derekfountain/zx-spectrum-lower-ram/__ATTIC/IMG_20221003_200314.jpg

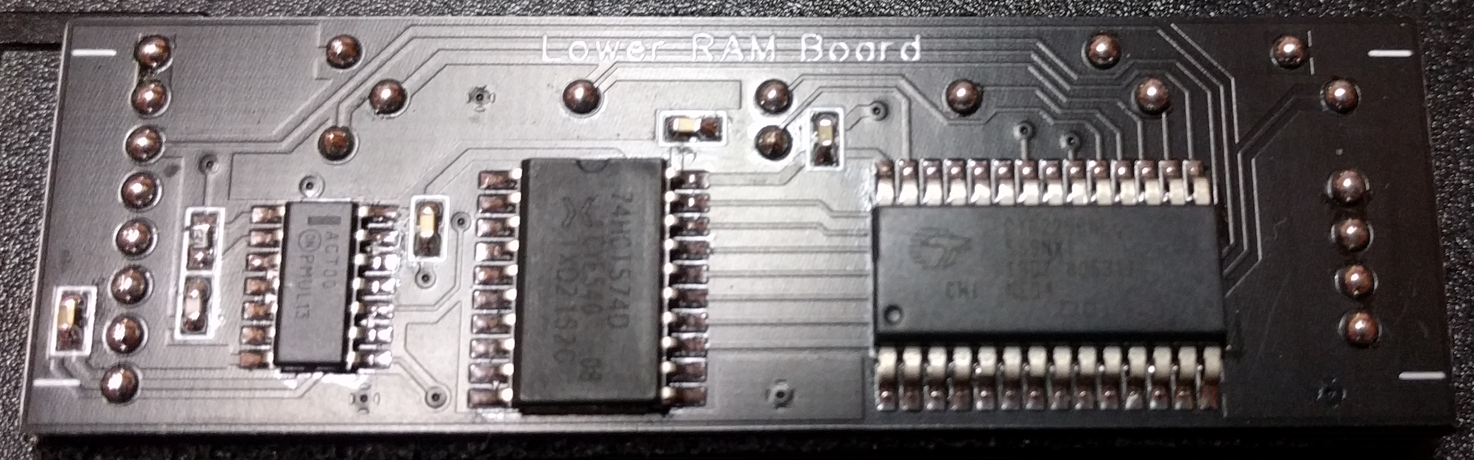
__ATTIC/IMG_20221003_200314.jpg
