derekfountain/zx-spectrum-lower-ram/__ATTIC/IMG_20221003_200335.jpg

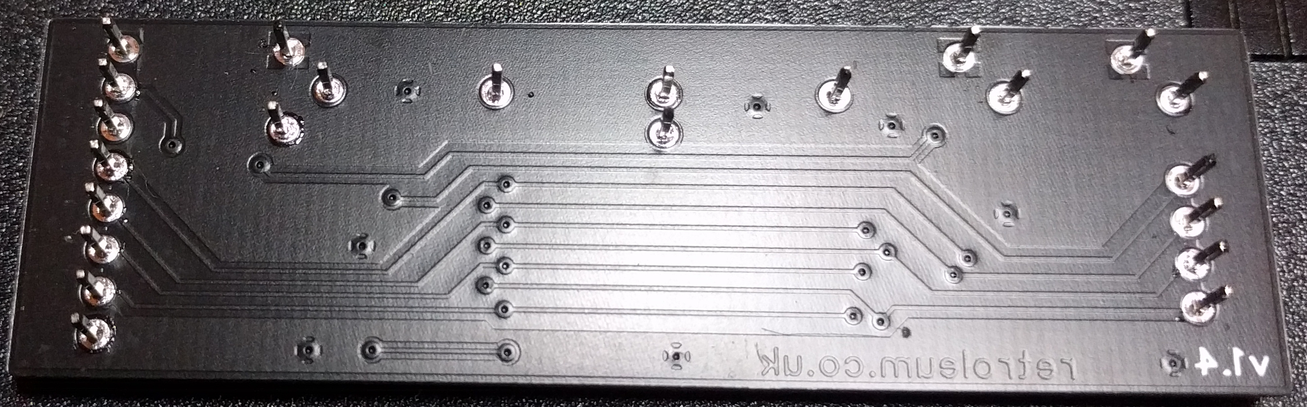
__ATTIC/IMG_20221003_200335.jpg
