derekfountain/zx-spectrum-lower-ram/__ATTIC/IMG_20221007_105308.jpg

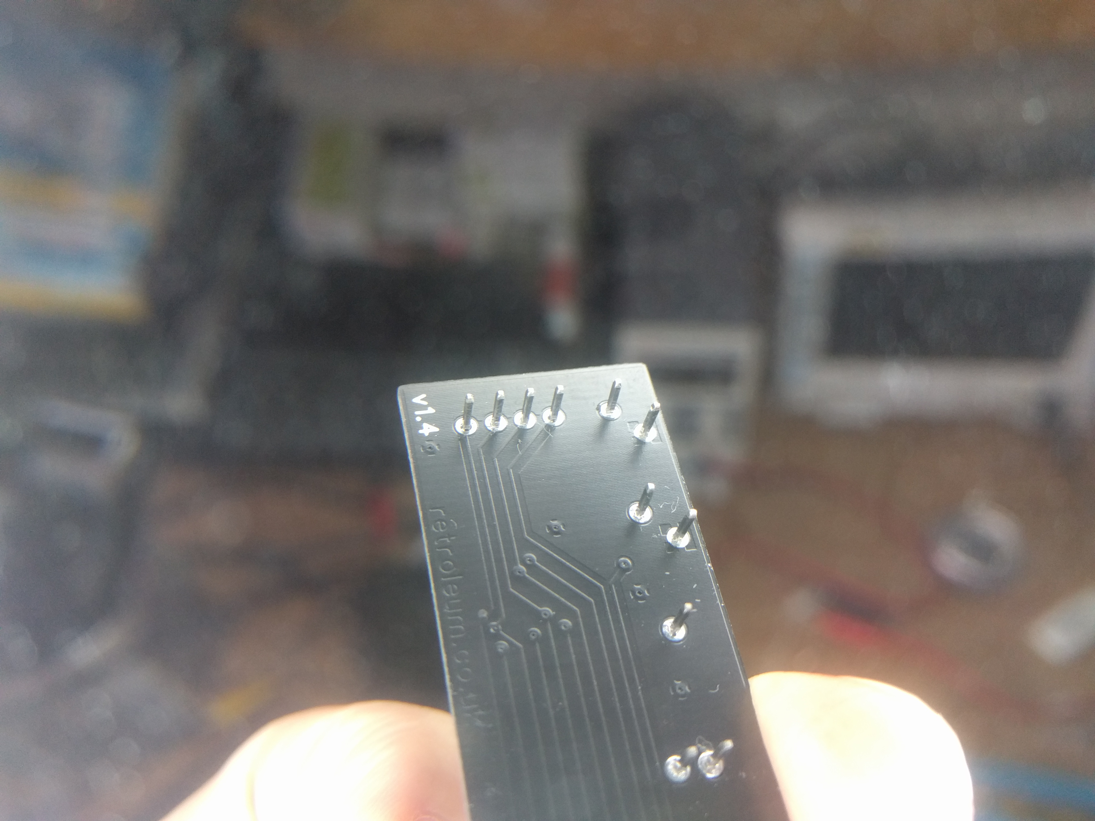
__ATTIC/IMG_20221007_105308.jpg
