derekfountain/zx-spectrum-lower-ram/__ATTIC/IMG_20221021_134358.jpg

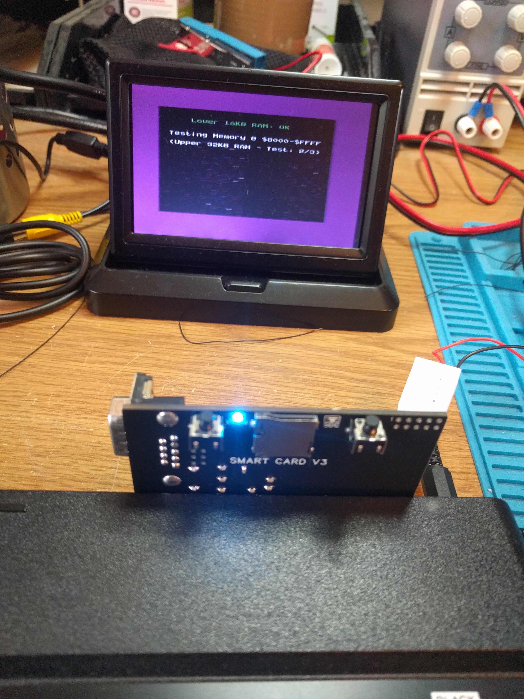
__ATTIC/IMG_20221021_134358.jpg
