derekfountain/zx-spectrum-lower-ram/__ATTIC/IMG_20221108_191128.jpg

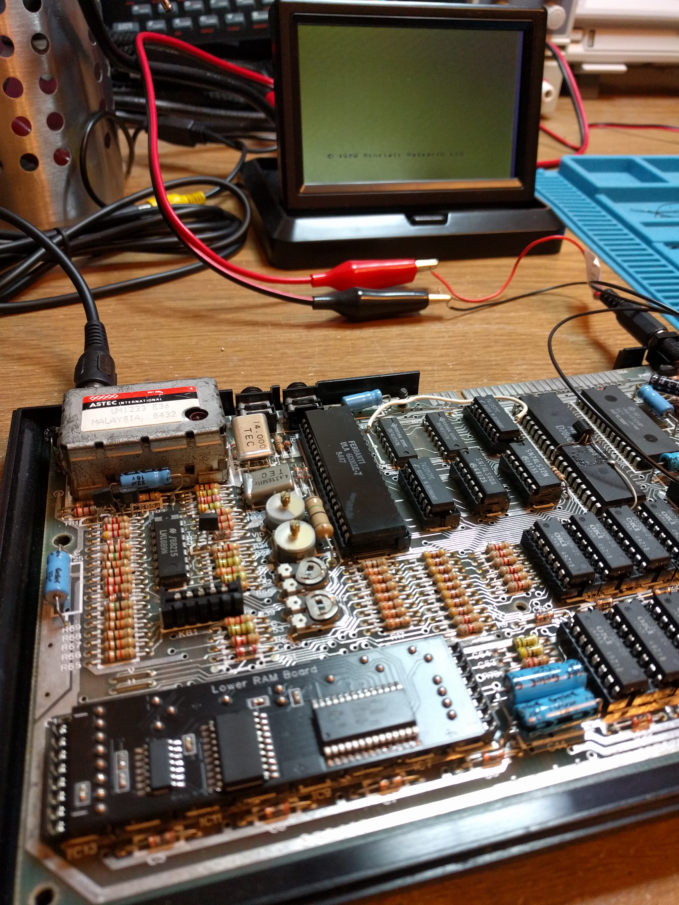
__ATTIC/IMG_20221108_191128.jpg
