derekfountain/zx-spectrum-lower-ram/Images/all_plastic_removed.jpg

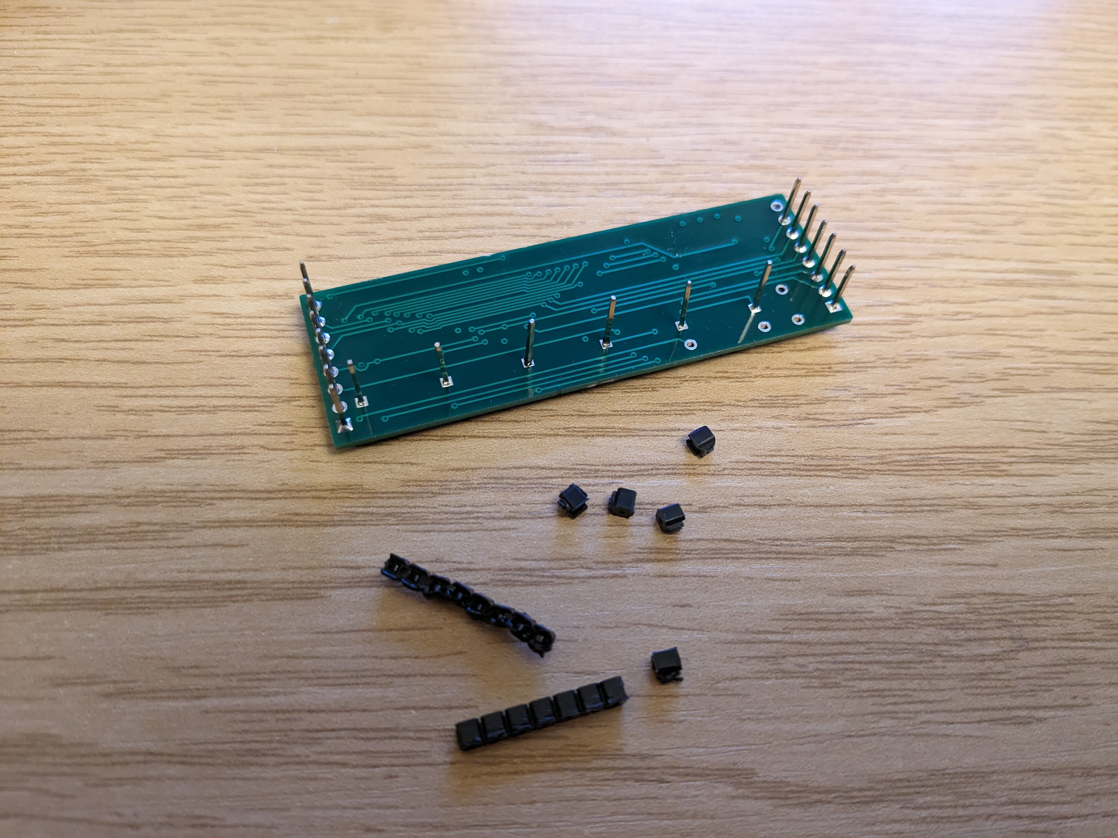
Images/all_plastic_removed.jpg
