derekfountain/zx-spectrum-lower-ram/Images/board_too_high.jpg

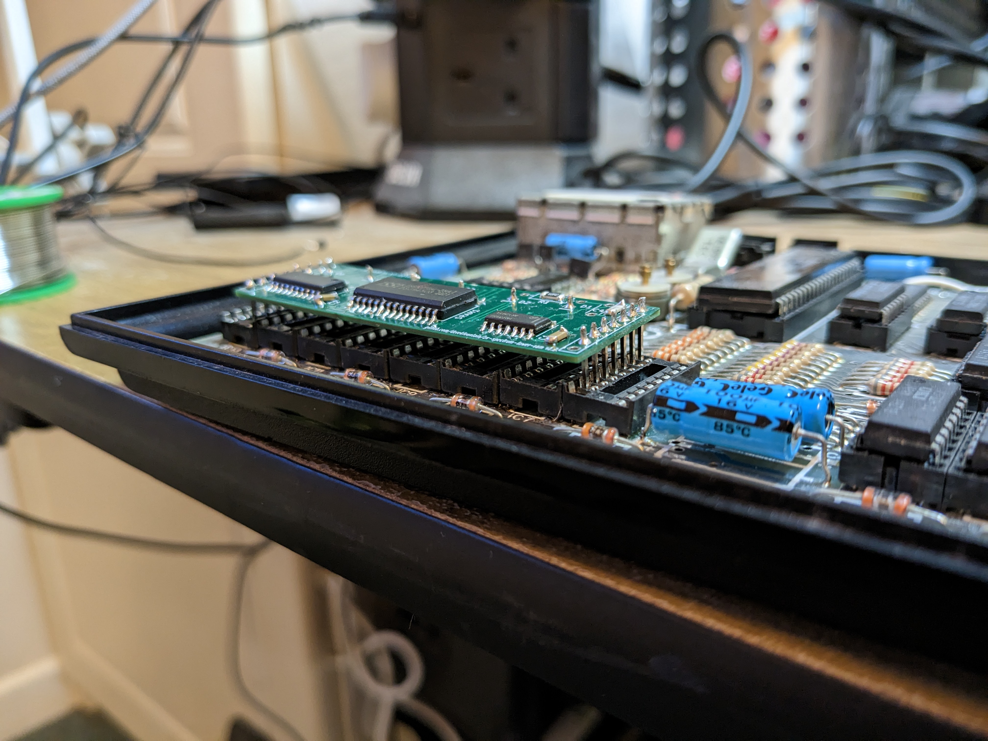
Images/board_too_high.jpg
