derekfountain/zx-spectrum-lower-ram/Images/board_too_high_sc.jpg

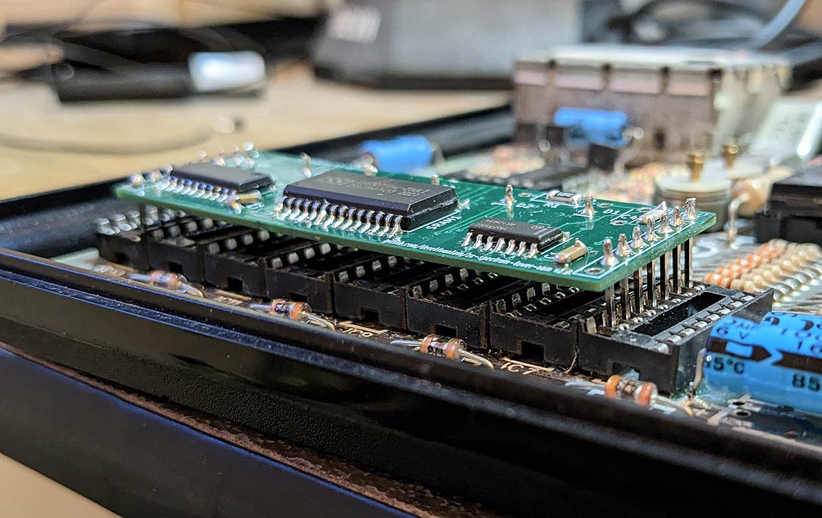
Images/board_too_high_sc.jpg
