derekfountain/zx-spectrum-lower-ram/Images/board_working_sc.jpg

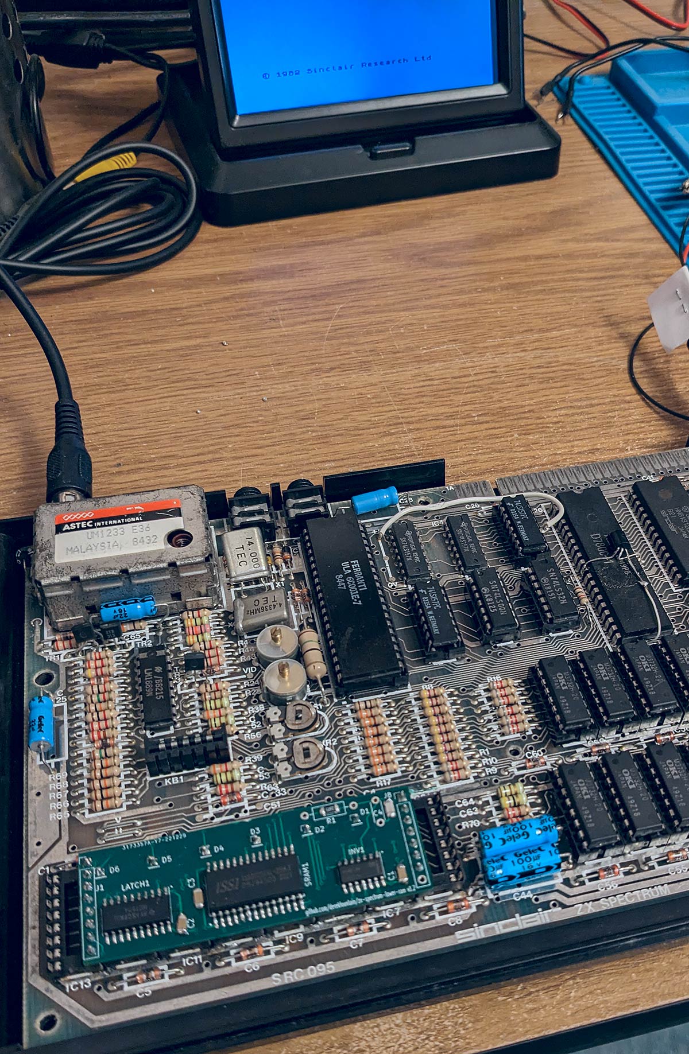
Images/board_working_sc.jpg
