derekfountain/zx-spectrum-lower-ram/Images/clip_headers.jpg

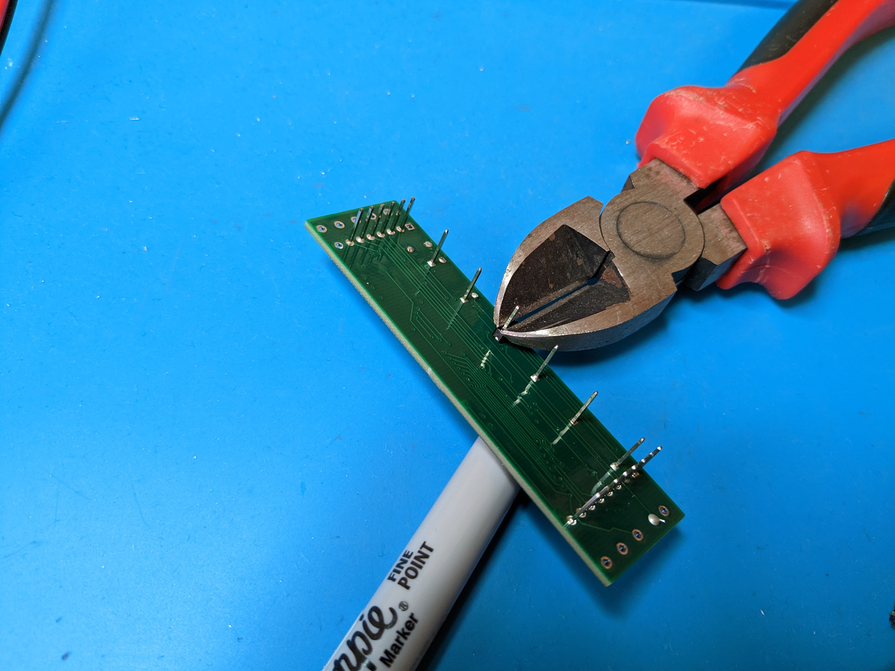
Images/clip_headers.jpg
