derekfountain/zx-spectrum-lower-ram/Images/clip_headers_sc.jpg

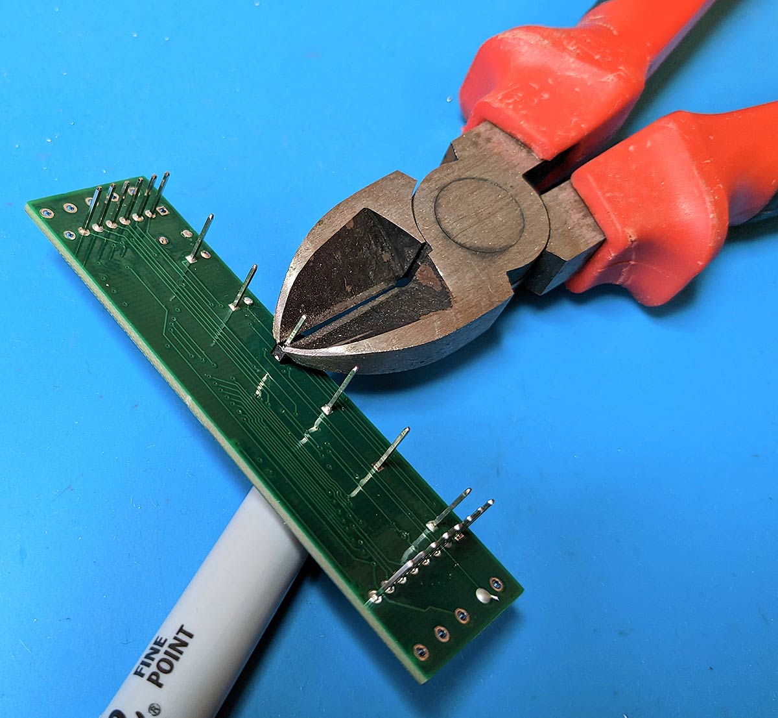
Images/clip_headers_sc.jpg
