derekfountain/zx-spectrum-lower-ram/Images/deplastic_headers.jpg

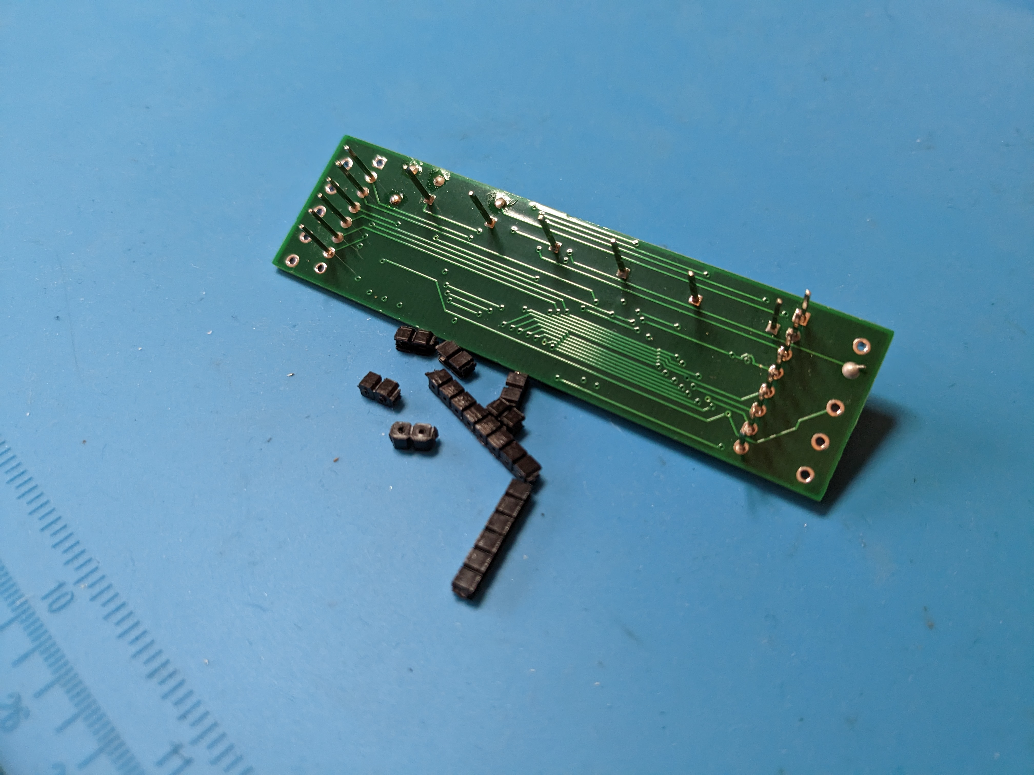
Images/deplastic_headers.jpg
