derekfountain/zx-spectrum-lower-ram/Images/dremel_pins.jpg

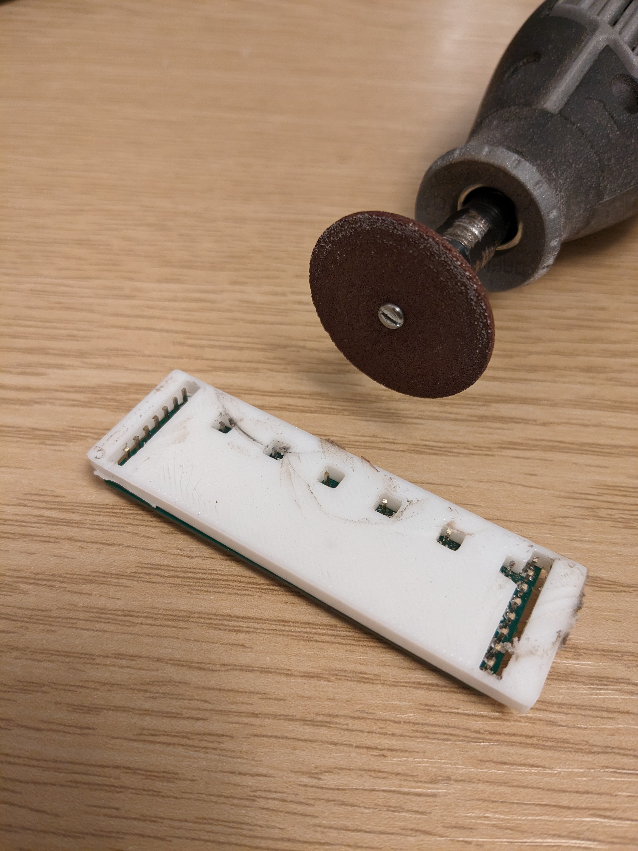
Images/dremel_pins.jpg
