derekfountain/zx-spectrum-lower-ram/Images/dremel_pins_sc.jpg

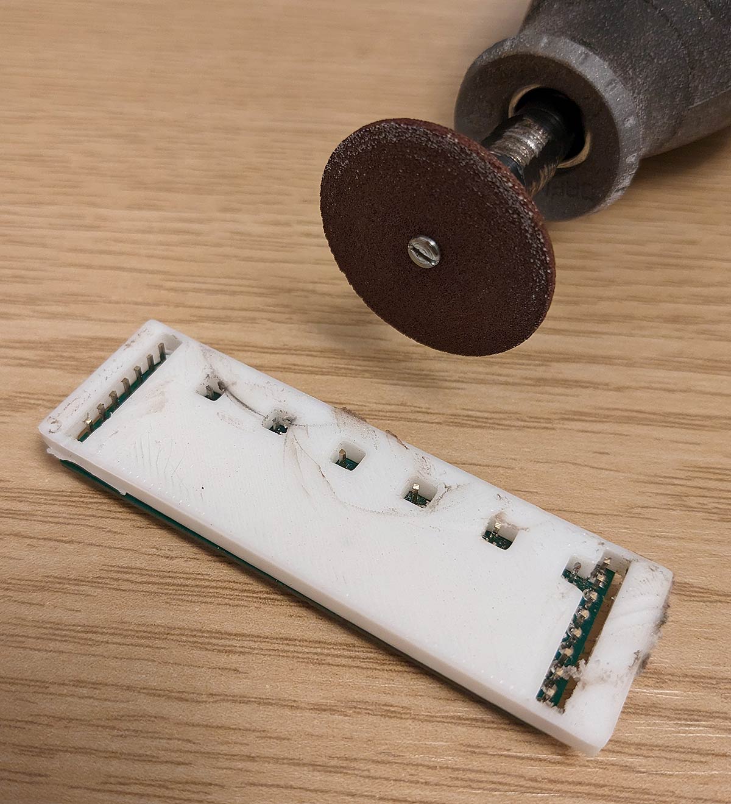
Images/dremel_pins_sc.jpg
