derekfountain/zx-spectrum-lower-ram/Images/final_board.jpg

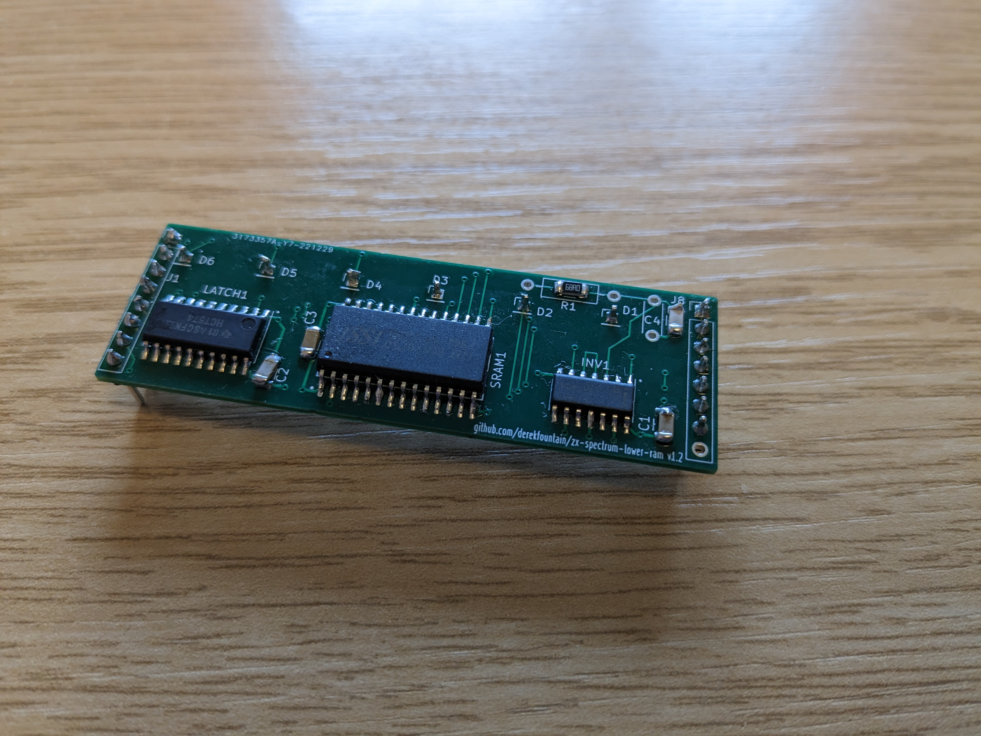
Images/final_board.jpg
