derekfountain/zx-spectrum-lower-ram/Images/final_board_sc.jpg

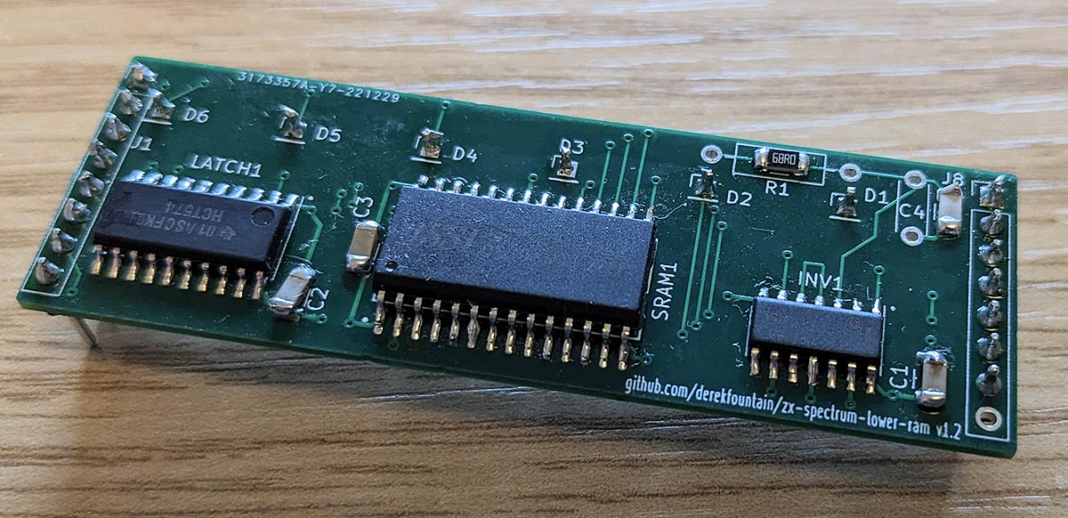
Images/final_board_sc.jpg
