derekfountain/zx-spectrum-lower-ram/Images/fixed_my_board.jpg

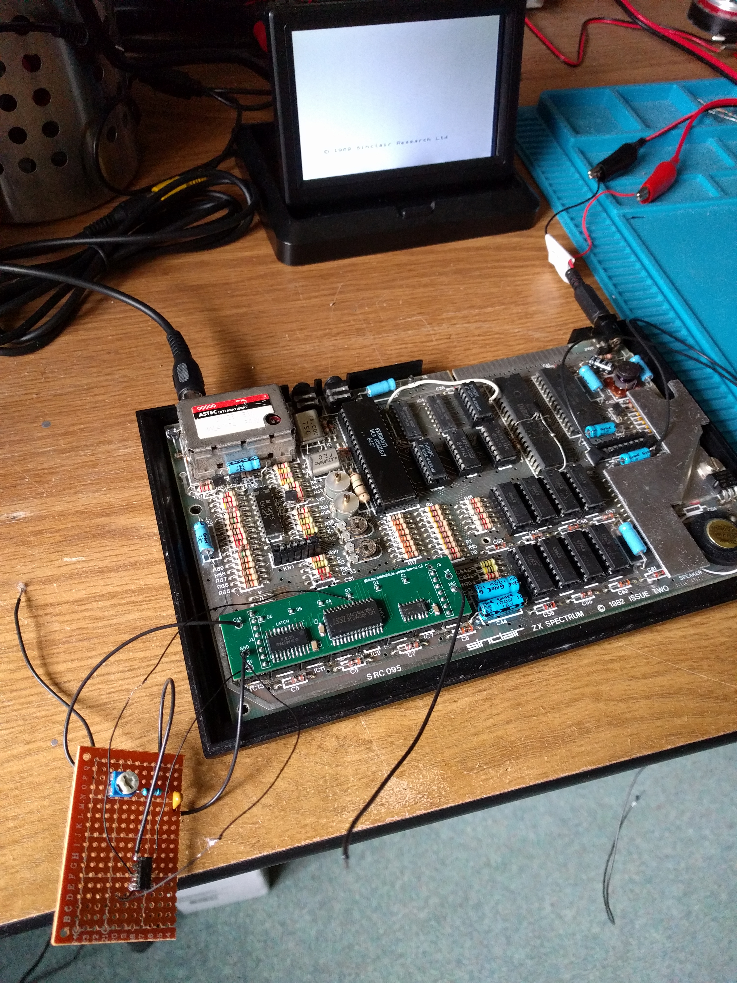
Images/fixed_my_board.jpg
