derekfountain/zx-spectrum-lower-ram/Images/fixed_my_board_sc.jpg

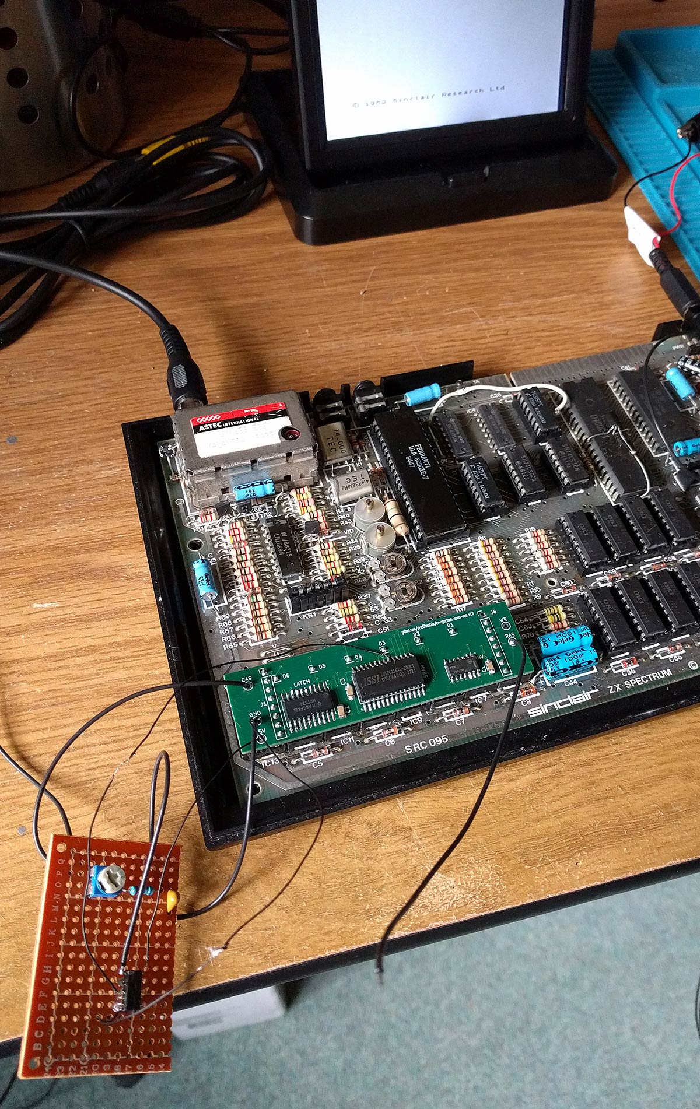
Images/fixed_my_board_sc.jpg
