derekfountain/zx-spectrum-lower-ram/Images/jig_in_place_sc.jpg

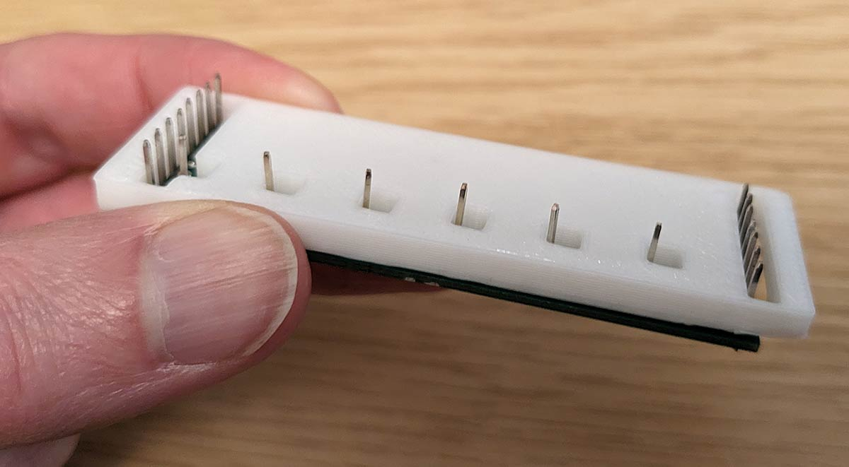
Images/jig_in_place_sc.jpg
