derekfountain/zx-spectrum-lower-ram/Images/keyboard_on_final.jpg

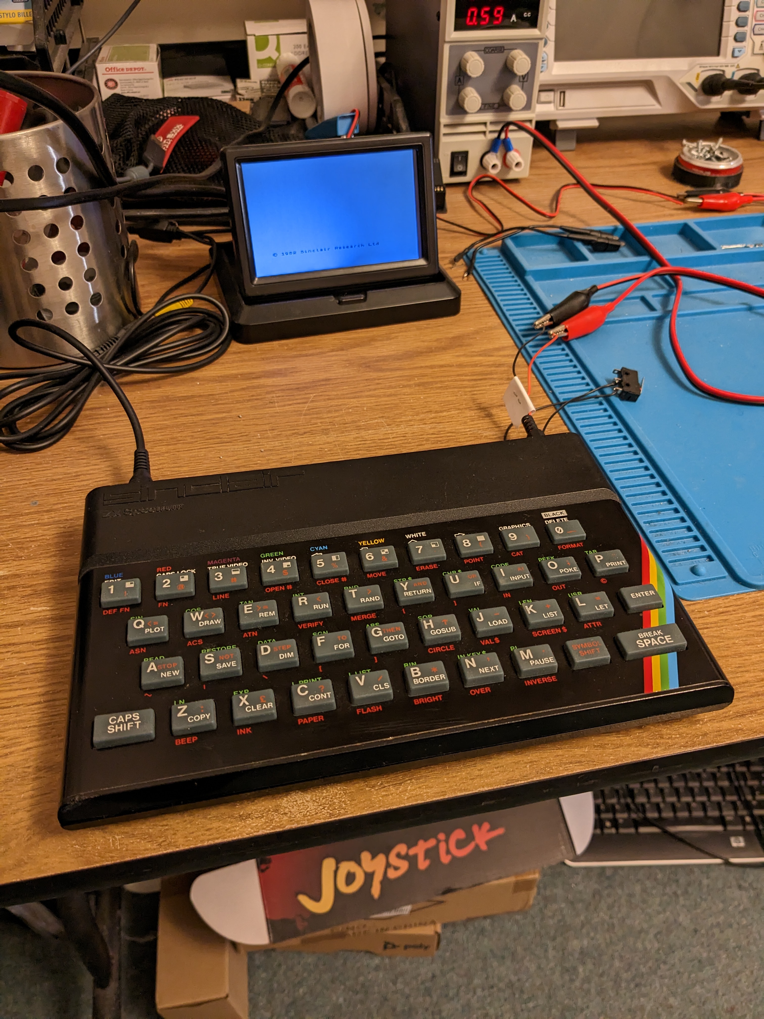
Images/keyboard_on_final.jpg
