derekfountain/zx-spectrum-lower-ram/Images/keyboard_on_final_sc.jpg

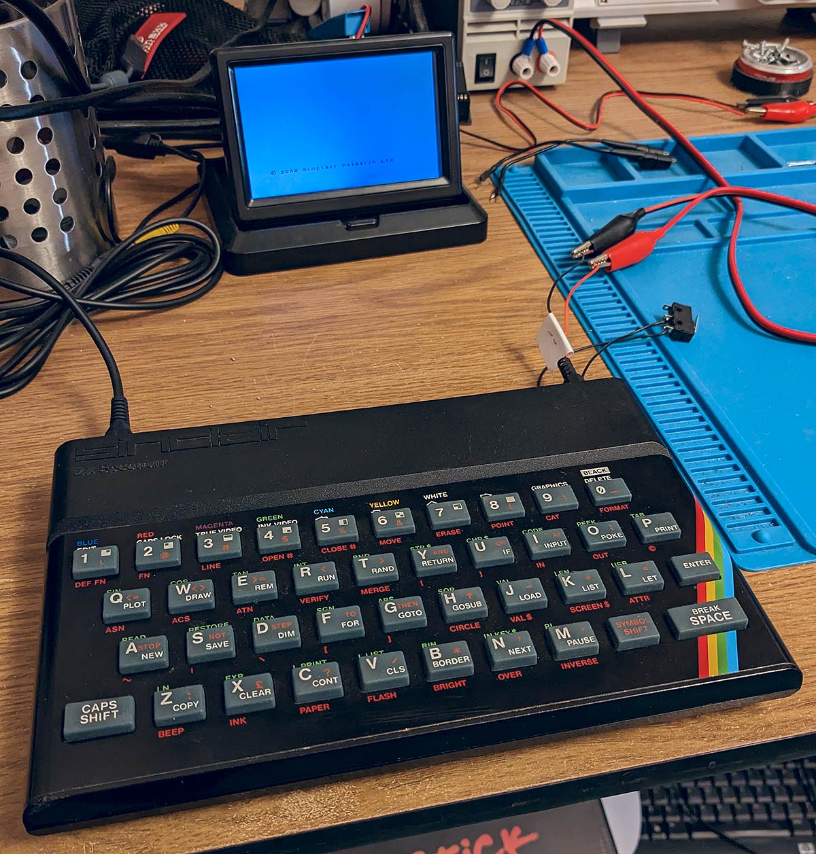
Images/keyboard_on_final_sc.jpg
