derekfountain/zx-spectrum-lower-ram/Images/pins_correct_sc.jpg

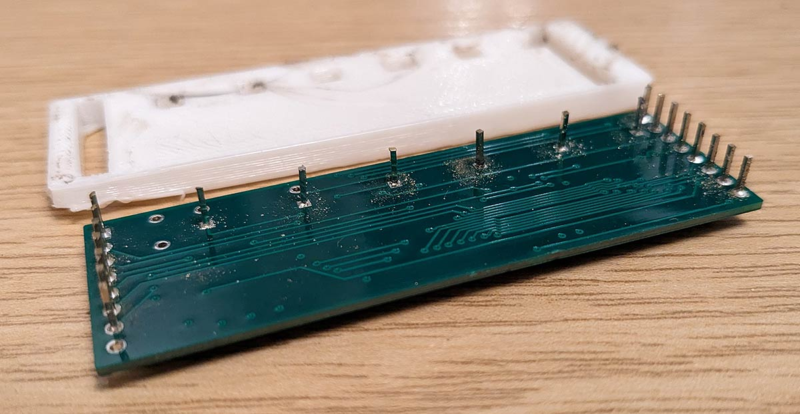
Images/pins_correct_sc.jpg
