derekfountain/zx-spectrum-lower-ram/Images/pins_too_long.jpg

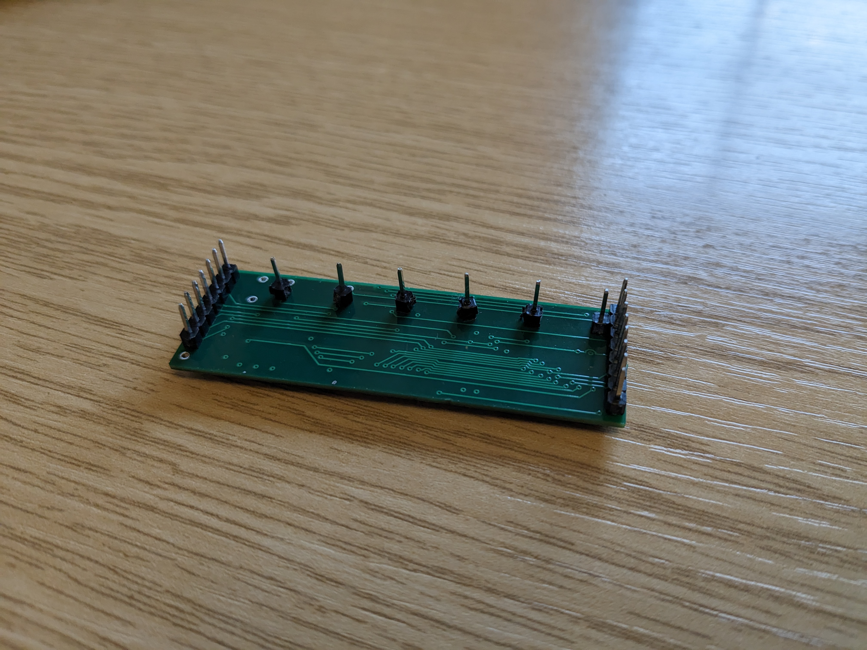
Images/pins_too_long.jpg
