derekfountain/zx-spectrum-lower-ram/Images/pins_too_long_sc.jpg

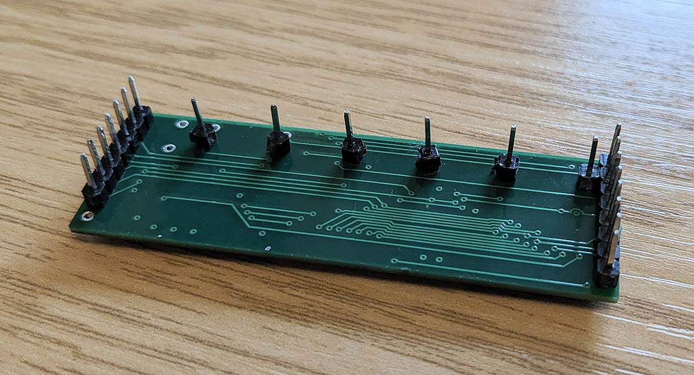
Images/pins_too_long_sc.jpg
