derekfountain/zx-spectrum-lower-ram/Images/prototype.jpg

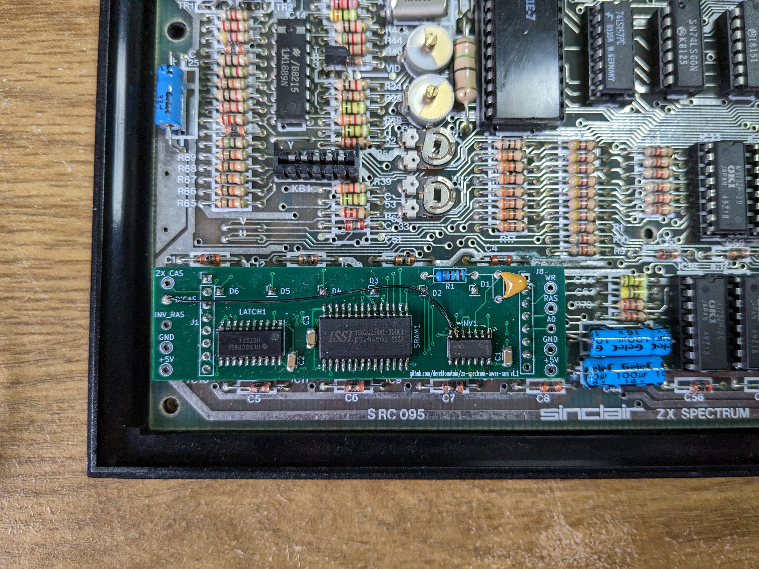
Images/prototype.jpg
