derekfountain/zx-spectrum-lower-ram/Images/prototype_sc.jpg

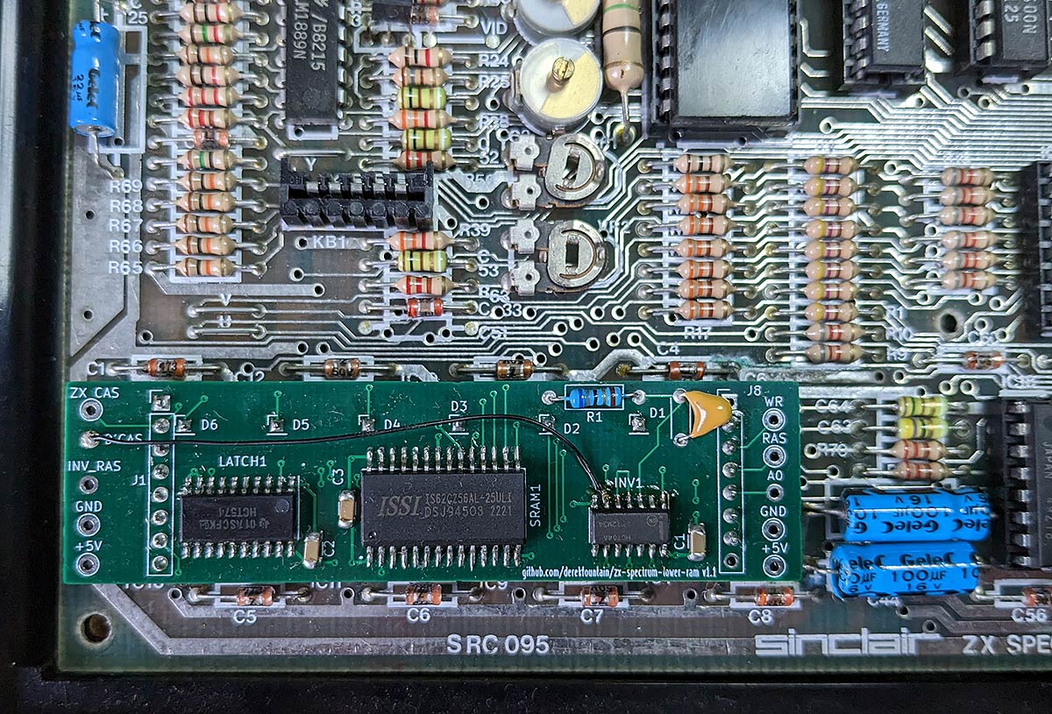
Images/prototype_sc.jpg
