derekfountain/zx-spectrum-lower-ram/Images/rc_mod.jpg

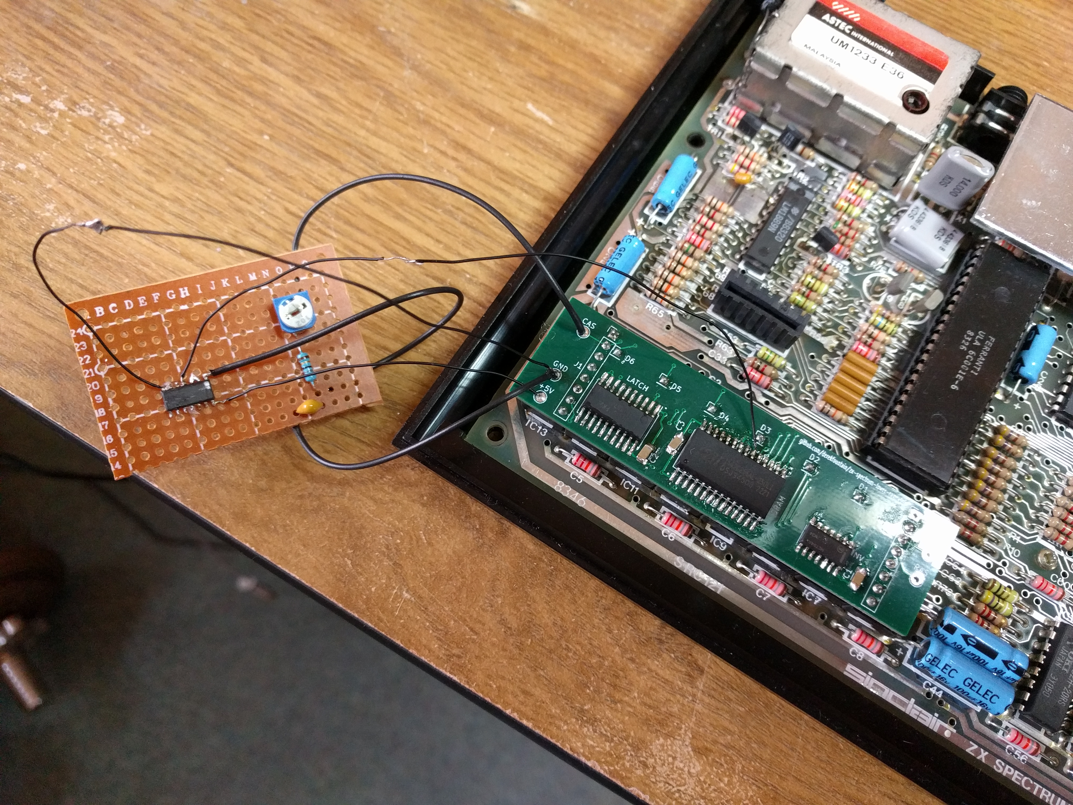
Images/rc_mod.jpg
