derekfountain/zx-spectrum-lower-ram/Images/rc_mod_sc.jpg

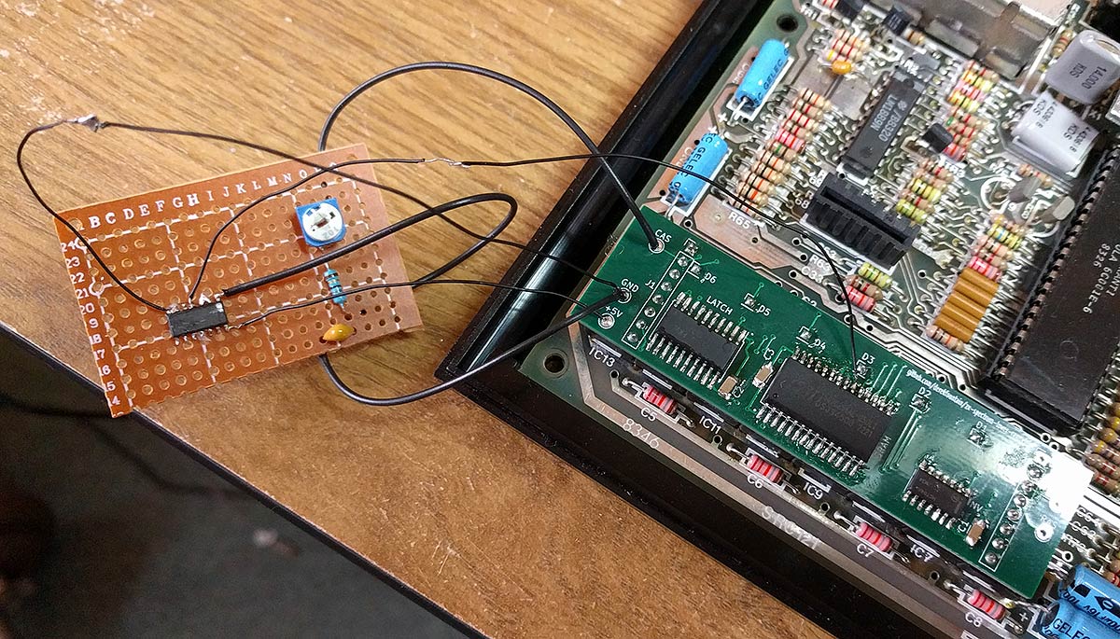
Images/rc_mod_sc.jpg
