derekfountain/zx-spectrum-lower-ram/Images/remove_plastic.jpg

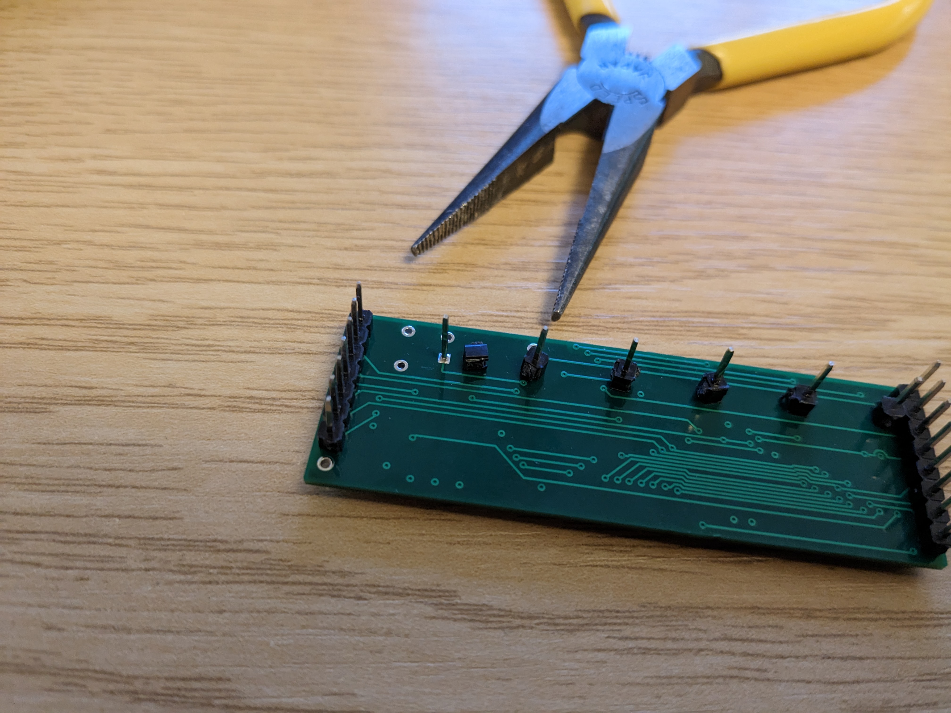
Images/remove_plastic.jpg
