derekfountain/zx-spectrum-lower-ram/Images/slrm-pcb.png

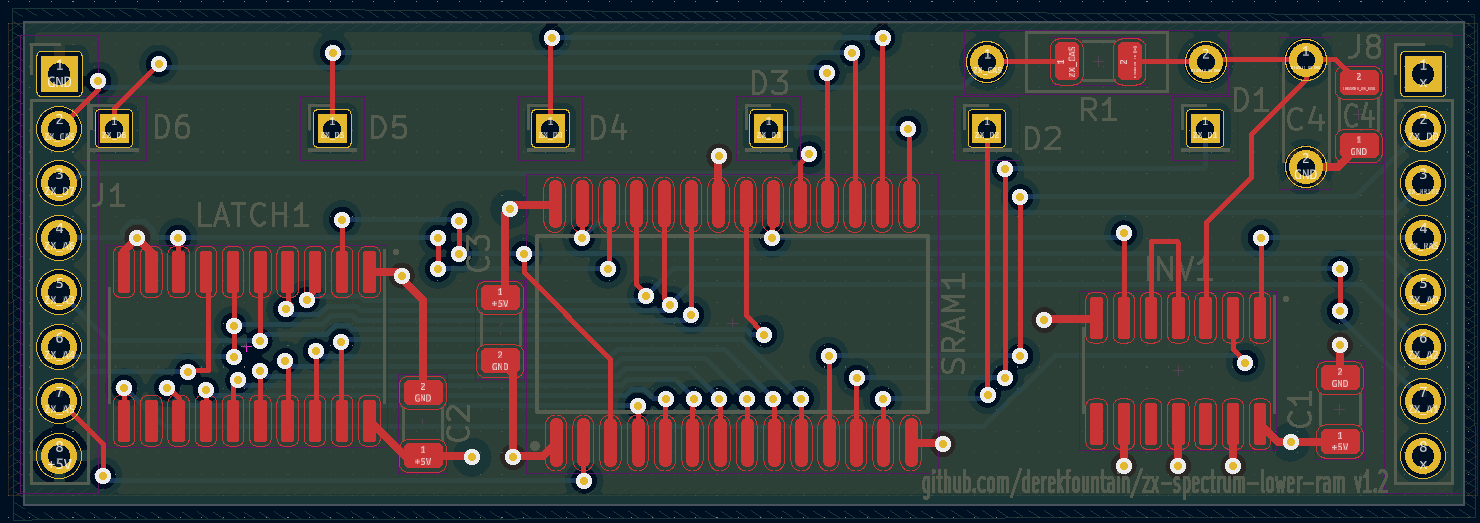
Images/slrm-pcb.png
