derekfountain/zx-spectrum-lower-ram/Images/v10_sparkles.jpg

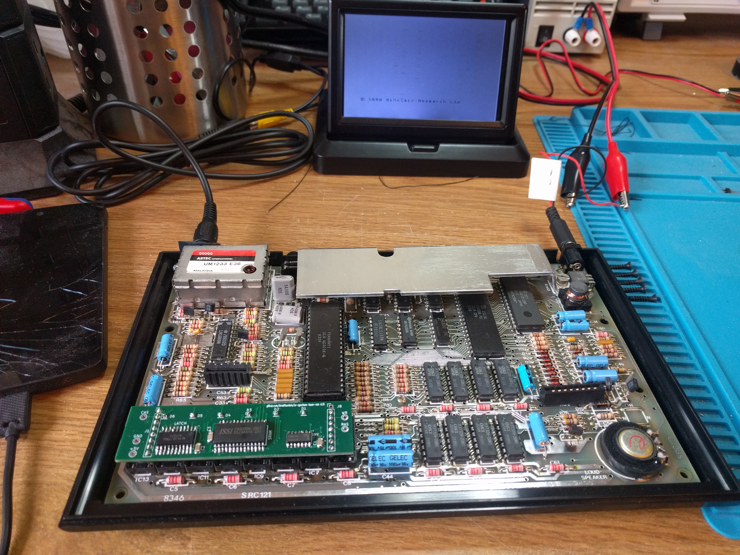
Images/v10_sparkles.jpg
