derekfountain/zx-spectrum-lower-ram/Images/v10_sparkles_sc.jpg

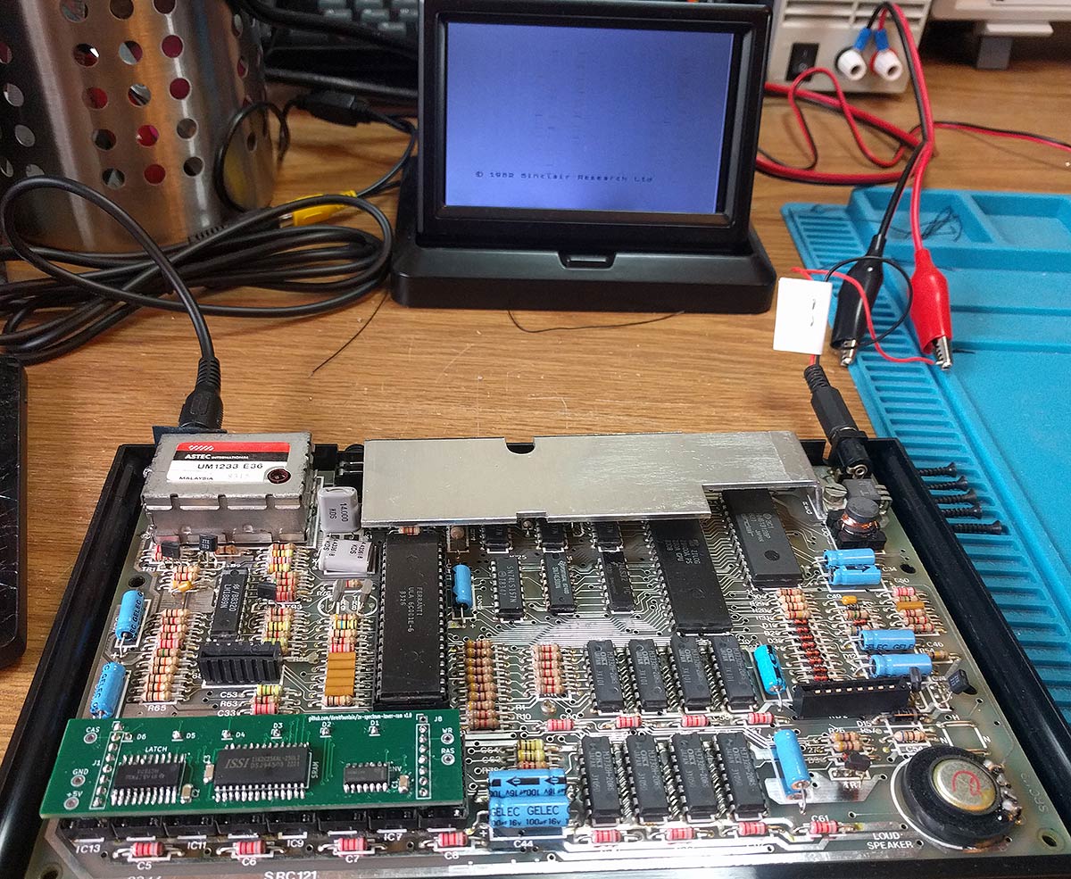
Images/v10_sparkles_sc.jpg
