derekfountain/zx-spectrum-lower-ram/__ATTIC/fixes/10K.png

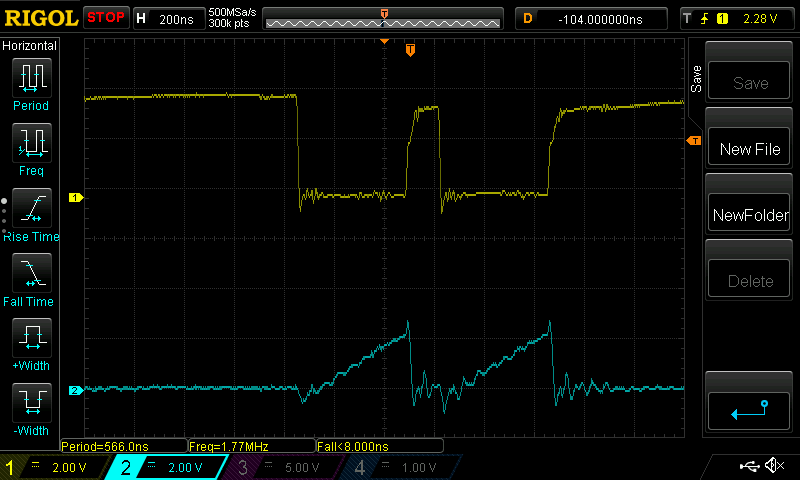
__ATTIC/fixes/10K.png
