derekfountain/zx-spectrum-lower-ram/__ATTIC/fixes/100R.png

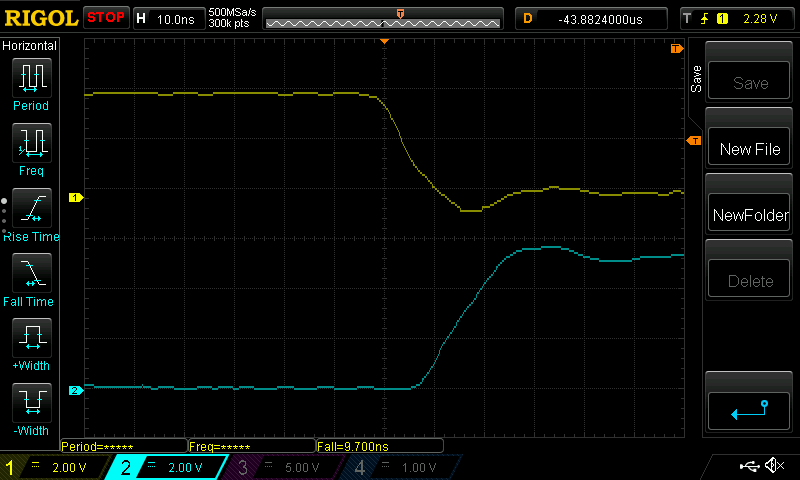
__ATTIC/fixes/100R.png
