derekfountain/zx-spectrum-lower-ram/__ATTIC/fixes/270R_1.png

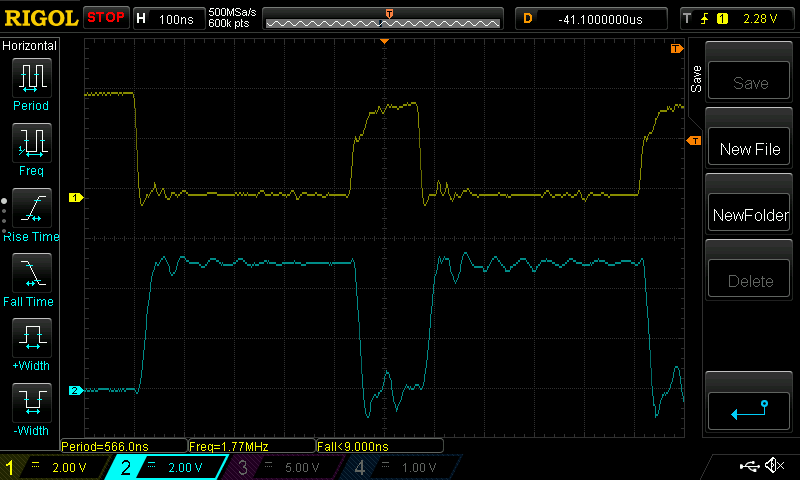
__ATTIC/fixes/270R_1.png
