derekfountain/zx-spectrum-lower-ram/__ATTIC/fixes/390R_1.png

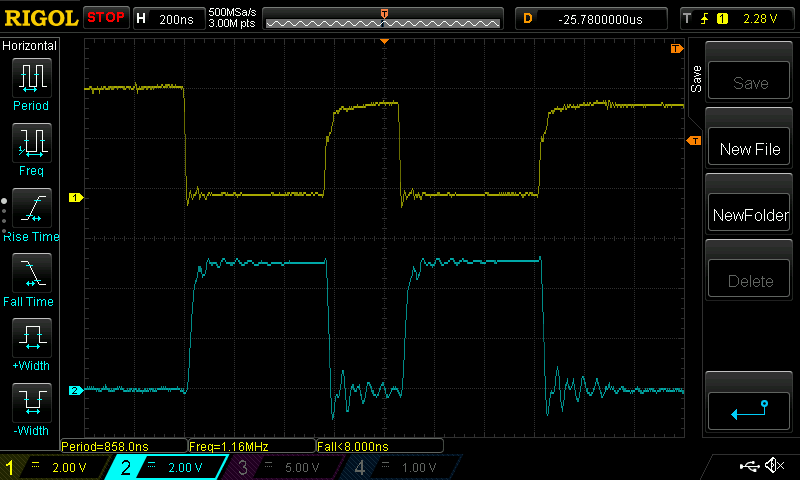
__ATTIC/fixes/390R_1.png
