derekfountain/zx-spectrum-lower-ram/__ATTIC/fixes/ard_rising_through_double_inv.png

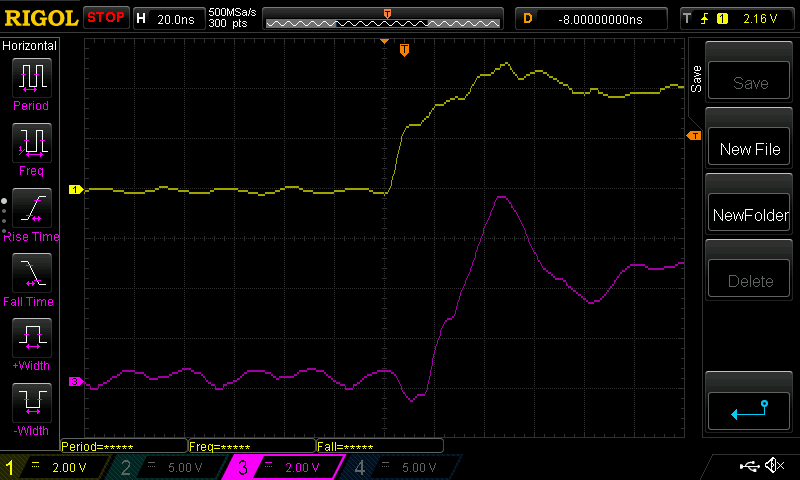
__ATTIC/fixes/ard_rising_through_double_inv.png
