derekfountain/zx-spectrum-lower-ram/__ATTIC/fixes/delayed_cas_330R_100_pF.png

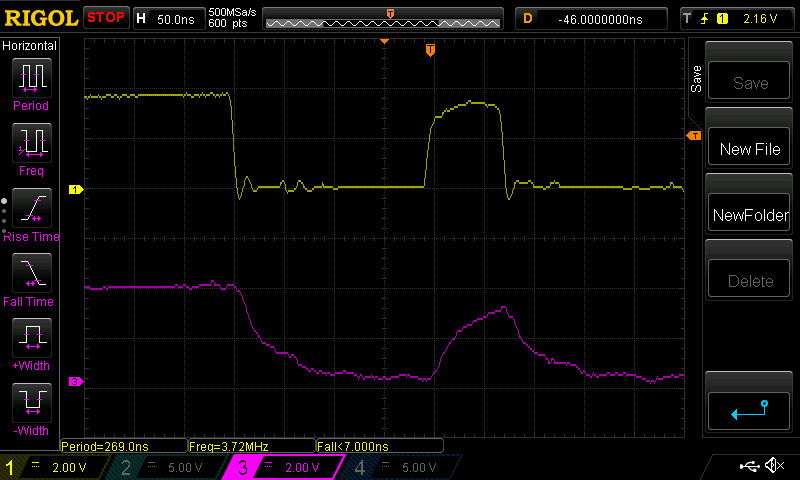
__ATTIC/fixes/delayed_cas_330R_100_pF.png
