derekfountain/zx-spectrum-lower-ram/__ATTIC/fixes/IMG_20221023_092814.jpg

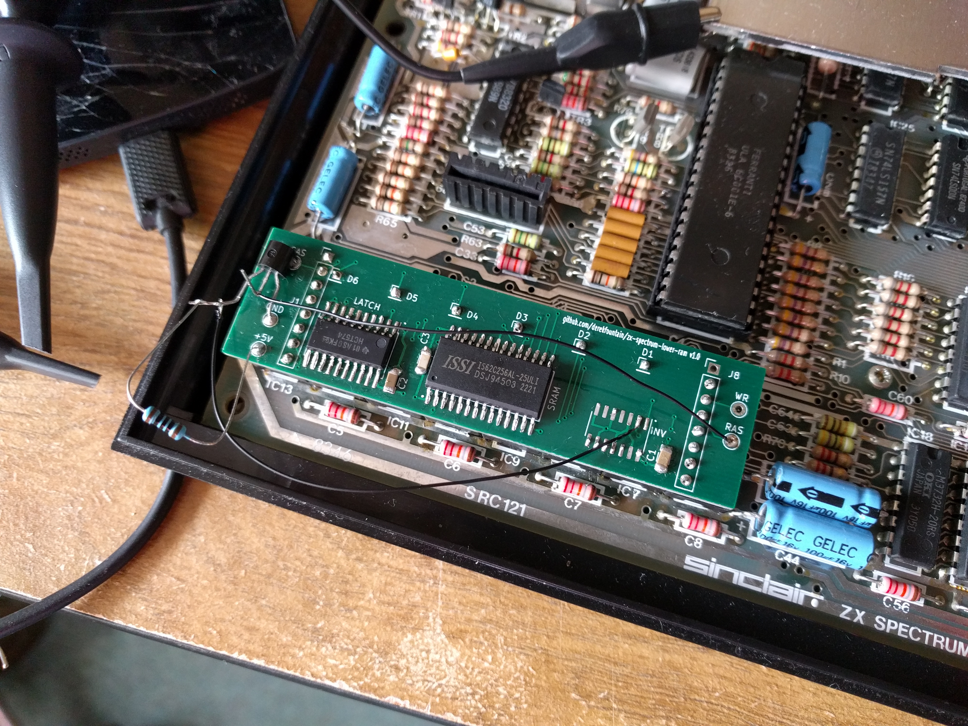
__ATTIC/fixes/IMG_20221023_092814.jpg
