derekfountain/zx-spectrum-lower-ram/__ATTIC/fixes/IMG_20221024_220533.jpg

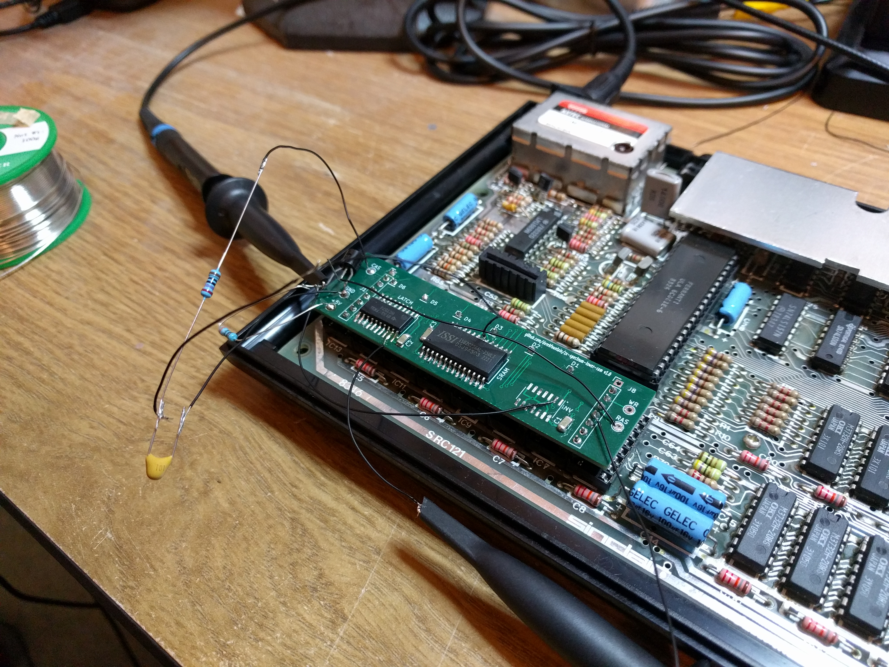
__ATTIC/fixes/IMG_20221024_220533.jpg
