derekfountain/zx-spectrum-lower-ram/__ATTIC/fixes/IMG_20221025_112422.jpg

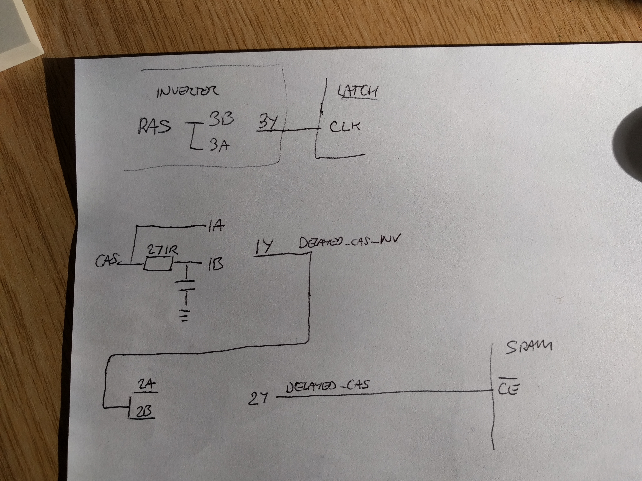
__ATTIC/fixes/IMG_20221025_112422.jpg
