derekfountain/zx-spectrum-lower-ram/__ATTIC/fixes/IMG_20221026_113512.jpg

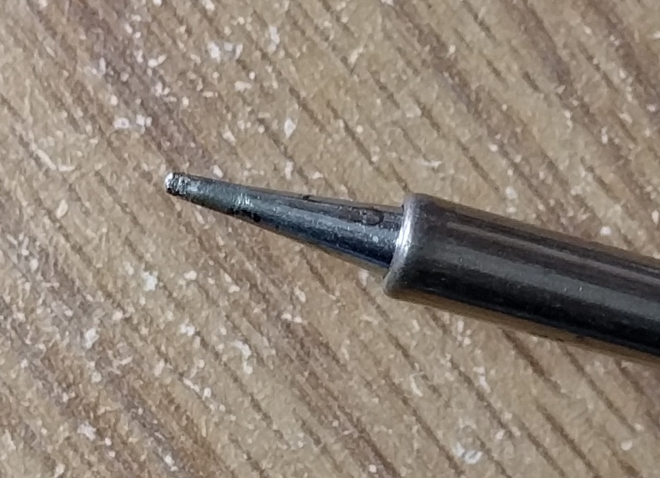
__ATTIC/fixes/IMG_20221026_113512.jpg
